jidantou/CEEReminder/Code/src/Process.c

// Process.c
#include "global.h"
#include "Process.h"
#include "GUI.h"
#include "DS1302.h"

uchar MonthDay[12] = {31, 28, 31, 30, 31, 30, 31, 31, 30, 31, 30, 31};

// debug
//uint debug = 10;

void Process()
{
	if(((CEEDAY[0] % 4 == 0) && (CEEDAY[0] % 100 != 0)) || (CEEDAY[0] % 400 == 0))
		MonthDay[1] = 29;
	else MonthDay[1] = 28;
}

void CountPro(uchar N)
{
	uint DaysCount, DaysNow, MinsCount, MinsNow, MinsDelta;
	DaysCount = Caldays(CountTime[N][6], CountTime[N][4], CountTime[N][3]);
	DaysNow = Caldays(Time[6], Time[4], Time[3]);
	MinsCount = CountTime[N][2] * 60 + CountTime[N][1];
	MinsNow = 60 * Time[2] + Time[1];

	if(CountPause[N] == 1)
		return;
	if((CountTime[N][6] < Time[6]) 
		|| (CountTime[N][6] == Time[6] && DaysCount < DaysNow) 
		|| (CountTime[N][6] == Time[6] && DaysCount == DaysNow && MinsCount <= MinsNow))
	{
		CountPause[N] = 1;
		CountDown[N][0] = 0;
		CountDown[N][1] = 0;
	}
	else 
	{
		MinsDelta = 1440 * (DaysCount - DaysNow);
		MinsDelta += MinsCount - MinsNow;
		CountDown[N][0] = MinsDelta / 60;
		CountDown[N][1] = MinsDelta % 60;
	}
}

// Short for KeyProcess
void KeyPro()
{
	uchar temp, count, i;
	
	if(CURSOR == 0x01)
		temp = 0;
	else if(CURSOR == 0x02)
		temp = 1;
	else if(CURSOR == 0x04)
		temp = 2;
	else temp = 3;

	if((ShowMode & 0x7F) == 3 || (ShowMode & 0x7F) == 10)
		count = 0;
	else if((ShowMode & 0x7F) == 4 || (ShowMode & 0x7F) == 11)
		count = 1;

	switch(ShowMode & 0x7F)
	{
	case 0:
	case 1:
	case 2:
	case 3:
	case 4:	
		if(KeySign & 0x01)		// Down
		{
			KeySign &= 0xFE;
			ShowMode++;
			ShowMode |= 0x80;
			if((ShowMode & 0x7F) >= 5)
				ShowMode = 0x80;
		}
		if(KeySign & 0x02)		// Up
		{
			KeySign &= 0xFD;
			if((ShowMode & 0x7F) == 0)
				ShowMode =0x84;
			else ShowMode--;
			ShowMode |= 0x80;
		}
		if(KeySign & 0x04)		// Memu
		{
			KeySign &= 0xFB;
			ShowMode = 0x85;
		}
		if(KeySign & 0x08)		// Enter
		{
			KeySign &= 0xF7;
			if((ShowMode & 0x7F) == 3 || (ShowMode & 0x7F) == 4)
			{
				if(CountPause[count] == 1)
				{
					CountTime[count][0] = 0;
					for(i = 0; i < 7; i++)
					{
						CountTime[count][i] = Time[i];
					}
					CountTime[count][1] += CountDown[count][1];
					CountTime[count][2] += CountDown[count][0];
					if(CountTime[count][1] >= 60)
					{
						CountTime[count][0]++;
						CountTime[count][1] -= 60;
						if(CountTime[count][2] >= 24)
						{
							CountTime[count][3]++;
							CountTime[count][2] -= 24;
							if(CountTime[count][3] > MonthDay[CountTime[count][4]] - 1)
							{
								CountTime[count][4]++;
								CountTime[count][3] = 1;
								if(CountTime[count][4] > 12)
								{
									CountTime[count][6]++;
									CountTime[count][4] -= 12;
								}
							}
						}
					}
				}
				CountPause[count] = CountPause[count] == 1 ? 0 : 1;
			}
		}
		break;
	case 5:
		if(KeySign & 0x01)		// Down
		{
			KeySign &= 0xFE;
			CURSOR <<= 1;
			if(CURSOR == 0x10)
			{
				ShowMode = 0x86;
				CURSOR = 0x01;
			}
			//ShowMode |= 0x80;
		}
		if(KeySign & 0x02)		// Up
		{
			KeySign &= 0xFD;
			if(CURSOR == 0x01)
			{
				ShowMode =0x86;
				CURSOR = 0x02;
			}
			else CURSOR >>= 1;
			//ShowMode |= 0x80;
		}
		if(KeySign & 0x04)		// Memu
		{
			KeySign &= 0xFB;
			ShowMode = 0x80;
			//debug = ShowMode;

			CURSOR = 0x01;
		}
		if(KeySign & 0x08)		// Enter
		{
			KeySign &= 0xF7;
			if(CURSOR == 0x01)
				ShowMode = 0x87;
			else if (CURSOR == 0x02)
				ShowMode = 0x88;
			else if(CURSOR == 0x04)
				ShowMode = 0x89;
			else if(CURSOR == 0x08)
			{
				ShowMode = 0x8A;
				CountPause[0] = 1;
			}
			CURSOR = 0x01;
		}
		break;
	case 6:
		if(KeySign & 0x01)		// Down
		{
			KeySign &= 0xFE;
            CURSOR <<= 1;
            if(CURSOR == 0x04)
            {
                ShowMode = 0x85;
                CURSOR = 0x01;
            }
		}
		if(KeySign & 0x02)		// Up
		{
            KeySign &=0xFD;
            if(CURSOR ==1)
            {
                ShowMode =0x85;
                CURSOR = 0x08;
            }
            else CURSOR >>= 1;
		}
		if(KeySign & 0x04)		// Memu
		{
            KeySign &= 0xFB;
            ShowMode = 0x80;
            CURSOR = 0x01;
		}
		if(KeySign & 0x08)		// Enter
		{
            KeySign &= 0xF7;
            if(CURSOR == 0x01)
			{
                ShowMode = 0x8B;
				CountPause[1] = 1;
			}
            else ShowMode = 0x80;
            CURSOR = 0x01;
		}
		break;
	case 7:
		if(KeySign & 0x01)		// Down
		{
			KeySign &= 0xFE;
			if(CURSOR == 0x01)
				if(CEEDAY[0] == 0)
					CEEDAY[0] = 99;
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
				}
			}
			if(CURSOR == 0x08)
			{
				CURSOR = 0x01;
				ShowMode = 0x85;
			}
		}
		break;
	}
}

void InterruptInit()
{
	// INT0
	IT0 = 1;
	EX0 = 1;
	// INT1
	IT1 = 1;
	EX1 = 1;
	// Timer0
	TMOD|=0X01;
	TH0=0XFC;  // 1ms
	TL0=0X18;
	ET0=1;

	// All interrupt
	EA=1;

}
